jeremynguyenn/NFC-Assisted-Self-Checkout-Cart-Hardware-and-Firmware/Project_Images/Energy_profiler_and_output_screenshots/bootid_mode1.PNG

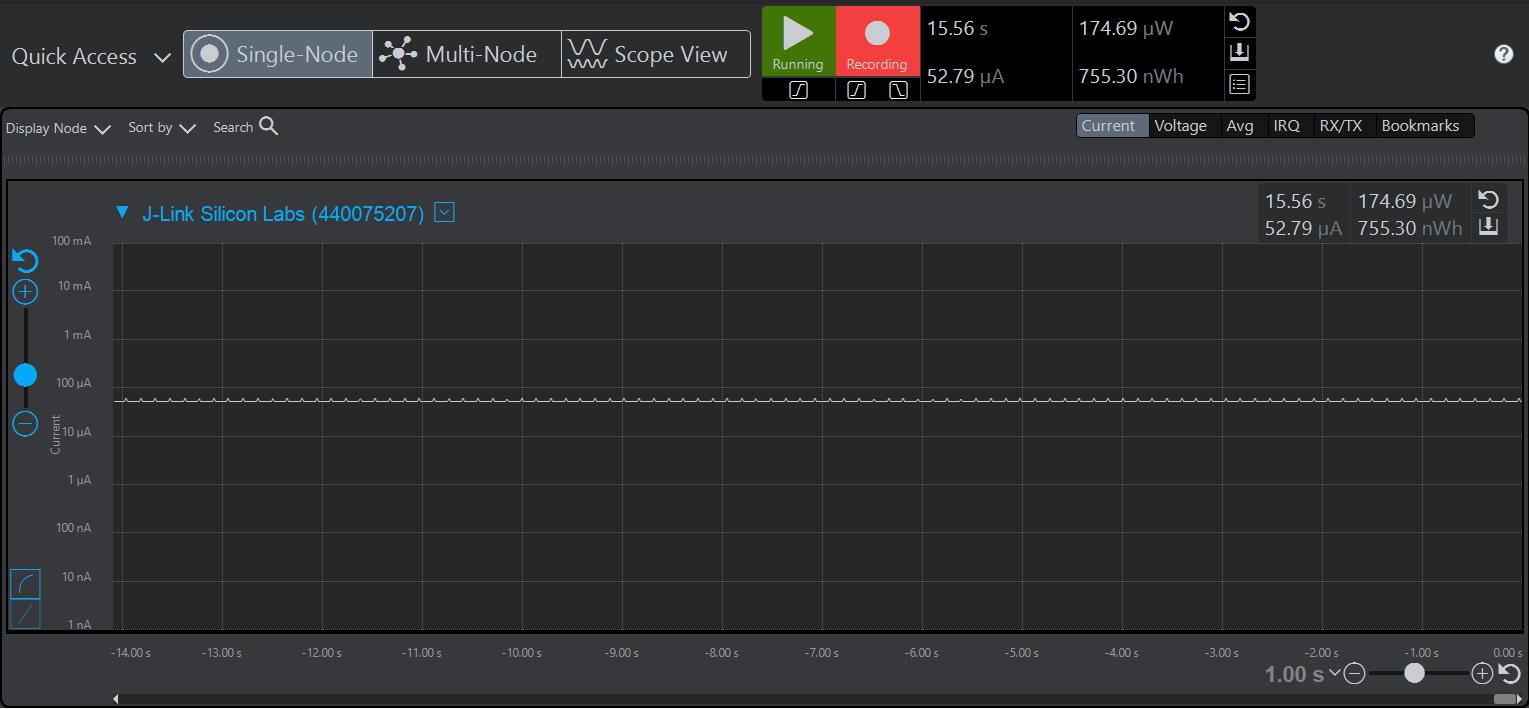
Project_Images/Energy_profiler_and_output_screenshots/bootid_mode1.PNG
