jeremynguyenn/NFC-Assisted-Self-Checkout-Cart-Hardware-and-Firmware/Project_Images/Energy_profiler_and_output_screenshots/nfcinterrupt_advertising_connection.PNG

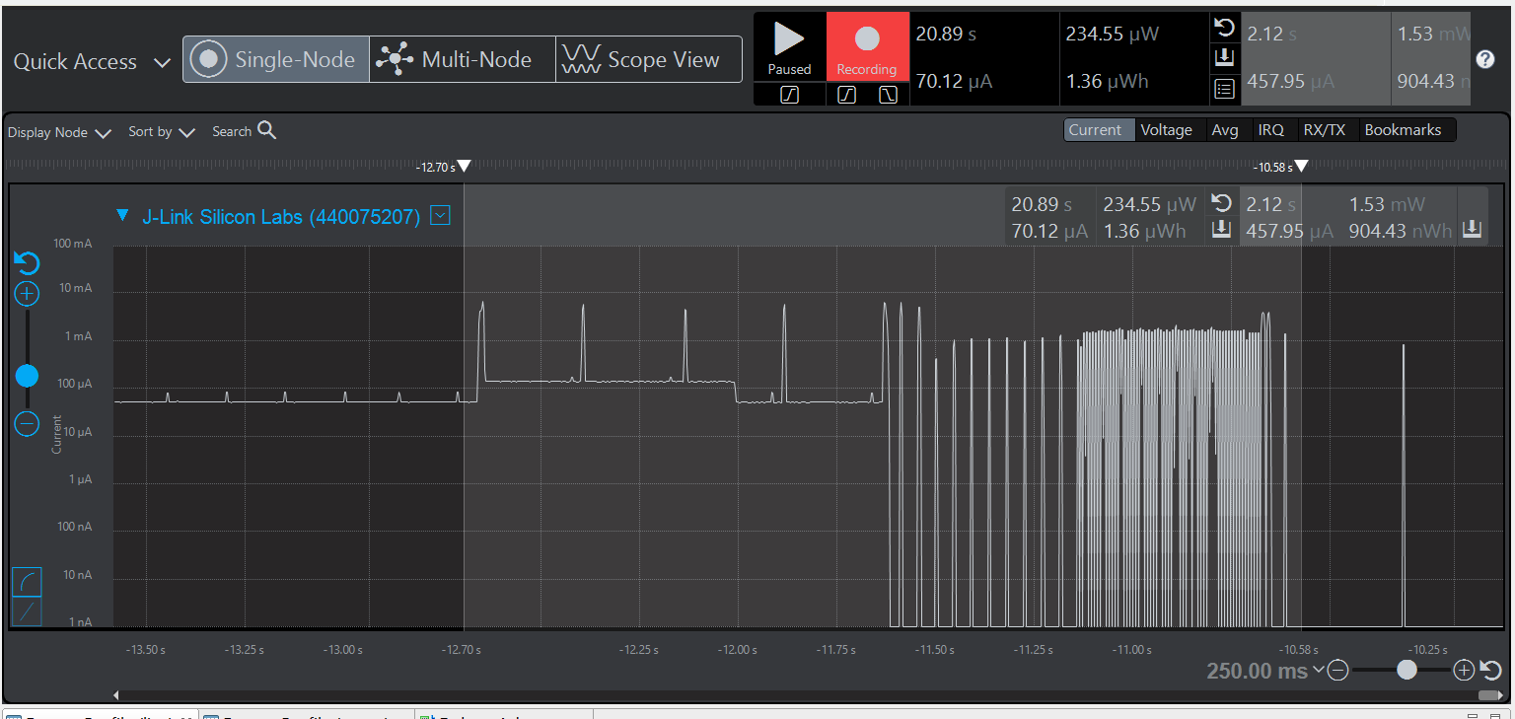
Project_Images/Energy_profiler_and_output_screenshots/nfcinterrupt_advertising_connection.PNG
