jeremynguyenn/NFC-Assisted-Self-Checkout-Cart-Hardware-and-Firmware/Project_Images/LPEDT-BLOCK-DIAGRAM01.jpg

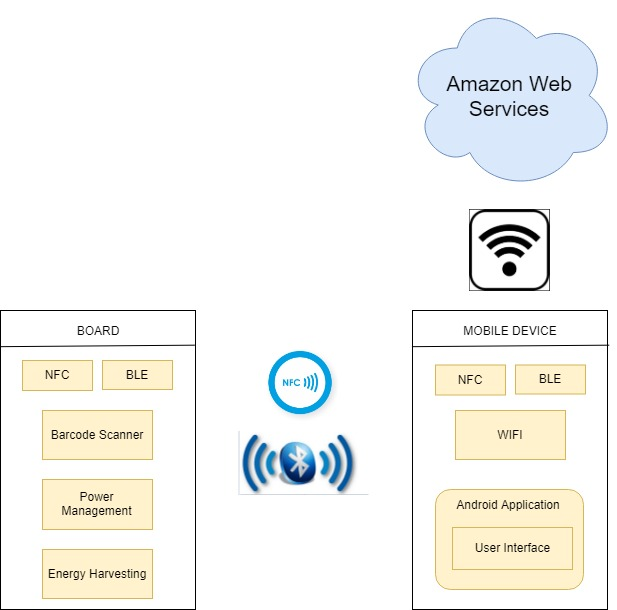
Project_Images/LPEDT-BLOCK-DIAGRAM01.jpg
