jeremynguyenn/NFC-Assisted-Self-Checkout-Cart-Hardware-and-Firmware/Project_Images/LPEDT-BLOCK-DIAGRAM-2-NEW.jpg

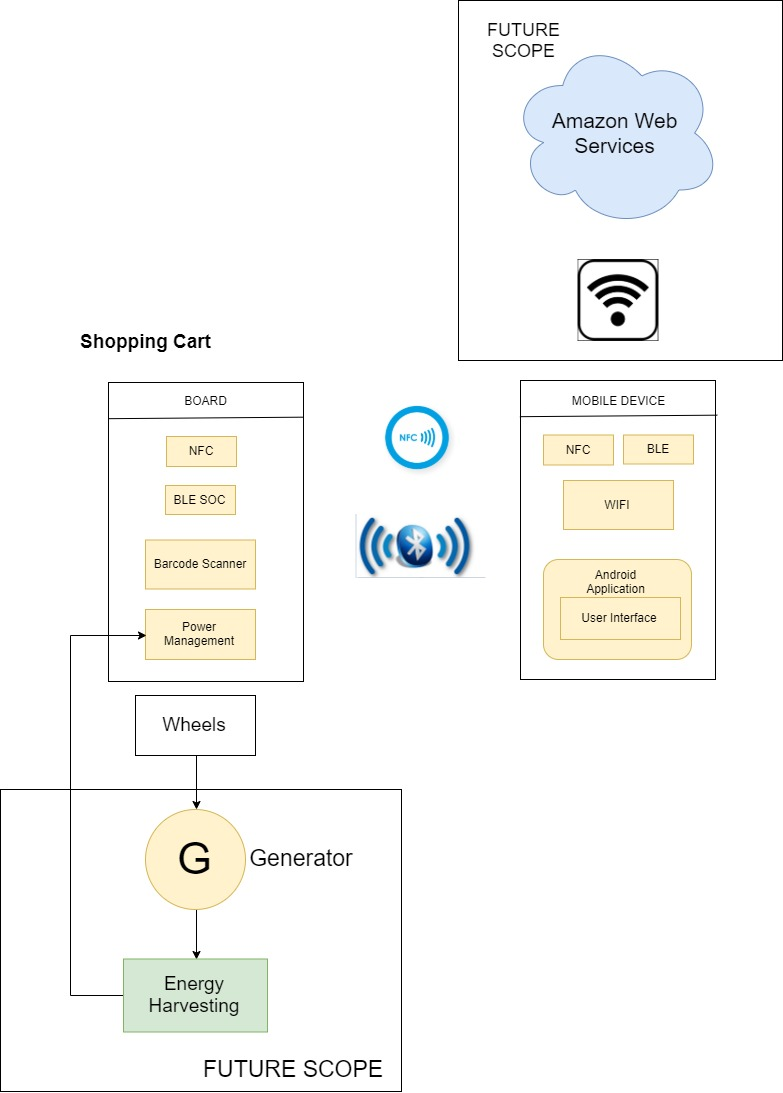
Project_Images/LPEDT-BLOCK-DIAGRAM-2-NEW.jpg
