jeremynguyenn/NFC-Assisted-Self-Checkout-Cart-Hardware-and-Firmware/Project_Images/LPEDT-BLOCK-DIAGRAM.jpg

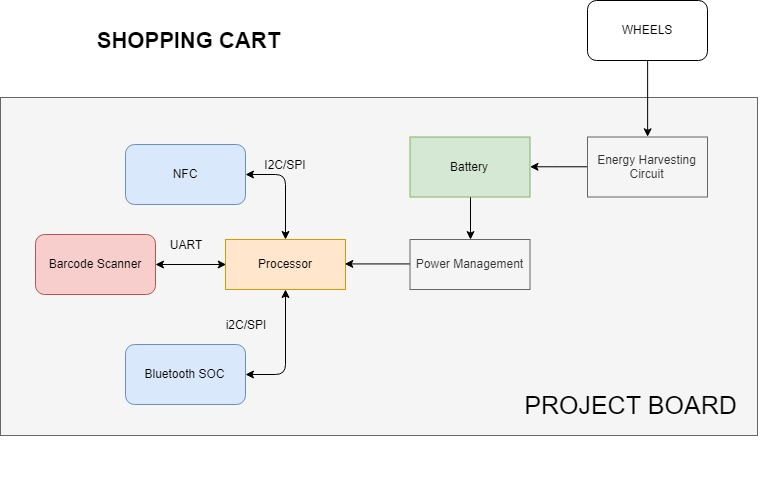
Project_Images/LPEDT-BLOCK-DIAGRAM.jpg
