jeremynguyenn/NFC-Assisted-Self-Checkout-Cart-Hardware-and-Firmware/Project_Images/LowPower_Verification/Peripherals/UART_LogicAnalyzer.png

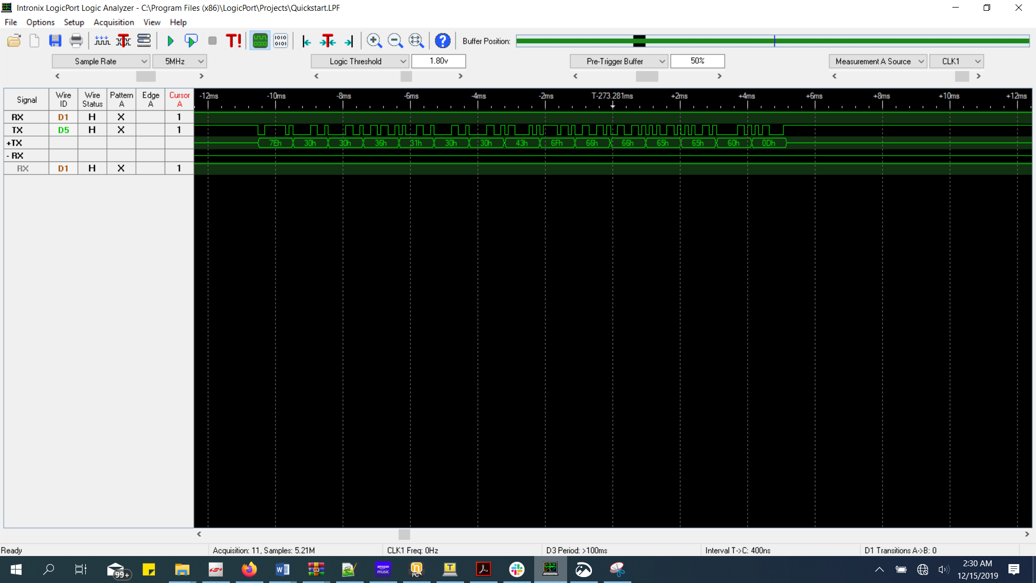
Project_Images/LowPower_Verification/Peripherals/UART_LogicAnalyzer.png
