jeremynguyenn/NFC-Assisted-Self-Checkout-Cart-Hardware-and-Firmware/Project_Images/LowPower_Verification/Power_Supply/BULK5V.jpg

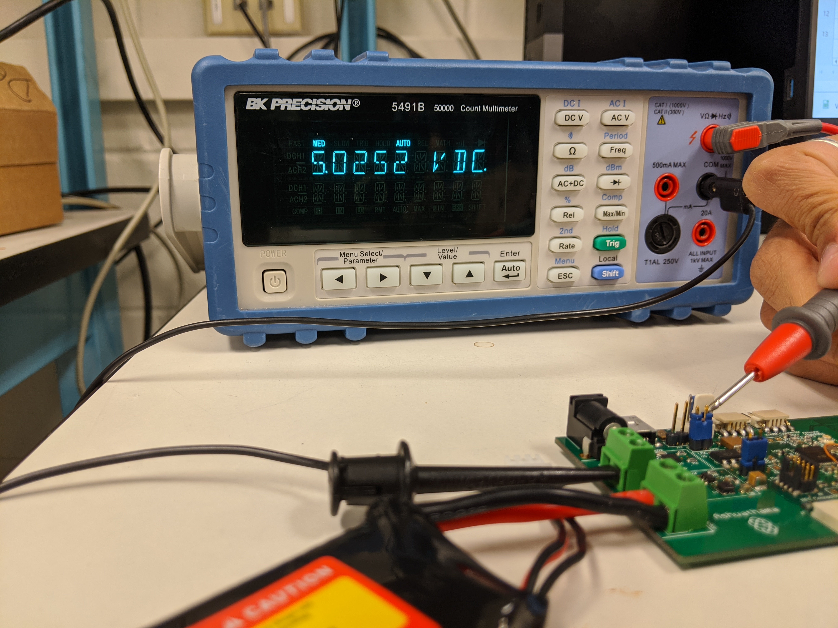
Project_Images/LowPower_Verification/Power_Supply/BULK5V.jpg
