jeremynguyenn/NFC-Assisted-Self-Checkout-Cart-Hardware-and-Firmware/Project_Images/LowPower_Verification/Power_Supply/USB3V3.jpg

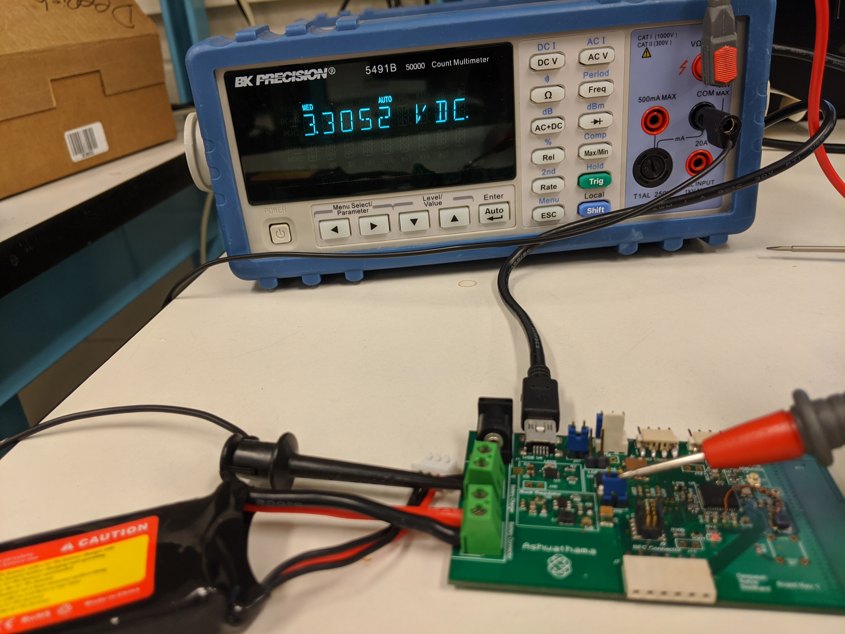
Project_Images/LowPower_Verification/Power_Supply/USB3V3.jpg
